amesclar/regattaTimer-Kicad/debugCodeSamples/simpleButtonTest.ino

// Use your existing definitions for BUZZER_PIN, BUZZ_LONG_MS, etc.
// You will need to copy the global buzzer state variables,
// the handleBuzzer() function, and the triggerBuzzSequence() function from the main code.

void setup() {
  Serial.begin(9600);
  pinMode(BUZZER_PIN, OUTPUT);
  digitalWrite(BUZZER_PIN, LOW);

  // Directly call the trigger for the 1-long buzz sequence
  Serial.println("Attempting to trigger 1 Long Buzz...");
  triggerBuzzSequence(1, 0);
  Serial.println("Buzzer state initialized.");
}

void loop() {
  // This is the only function running in the loop
  handleBuzzer(millis());
}
